AAUSmartProductionLab/data-driven-decisions/figures/structure.png

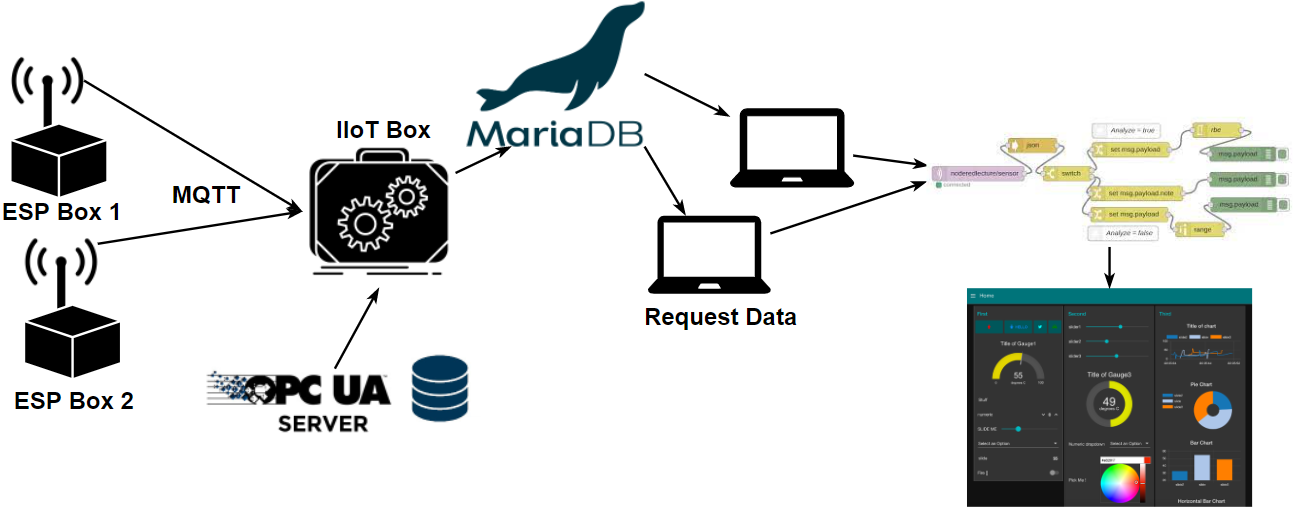
figures/structure.png
